HorstBaerbel/HubAlyzer/HubAlyzer/approx.h

#pragma once

#include <utility>
#include <cmath>

// == 1 / log2(10)
#define ONE_OVER_LOG2_10 0.3010299956639812f

// compute log10(x) by reducing x to [0.75, 1.5), then divide by log2(10)
// See: https://tech.ebayinc.com/engineering/fast-approximate-logarithms-part-iii-the-formulas/
// This version uses only multiplies
float log10f_fast(float x)
{
    constexpr float a = 0.338531;
    constexpr float b = -0.741619;
    constexpr float c = 1.445866;
#define FNM fexp + (((a * signif) + b) * signif + c) * signif

    float signif, fexp;
    int exp;
    float lg2;
    union {
        float f;
        unsigned int i;
    } ux1, ux2;
    int greater; // really a boolean
    /* 
     * Assume IEEE representation, which is sgn(1):exp(8):frac(23)
     * representing (1+frac)*2^(exp-127).  Call 1+frac the significand
     */

    // get exponent
    ux1.f = x;
    exp = (ux1.i & 0x7F800000) >> 23;
    // actual exponent is exp-127, will subtract 127 later

    greater = ux1.i & 0x00400000; // true if signif > 1.5
    if (greater)
    {
        // signif >= 1.5 so need to divide by 2.  Accomplish this by
        // stuffing exp = 126 which corresponds to an exponent of -1
        ux2.i = (ux1.i & 0x007FFFFF) | 0x3f000000;
        signif = ux2.f;
        fexp = exp - 126; // 126 instead of 127 compensates for division by 2
        signif = signif - 1.0;
        lg2 = FNM;
    }
    else
    {
        // get signif by stuffing exp = 127 which corresponds to an exponent of 0
        ux2.i = (ux1.i & 0x007FFFFF) | 0x3f800000;
        signif = ux2.f;
        fexp = exp - 127;
        signif = signif - 1.0;
        lg2 = FNM;
    }
    // last two lines of each branch are common code, but optimize better
    // when duplicated, at least when using gcc
    return lg2 * ONE_OVER_LOG2_10;
}

// Compute sin(x) and cos(x) with x in radians
std::pair<float, float> sincosf_fast(float x)
{
    // 256 sine values + 64 for cosine + one value added to front and back for safe interpolation
    static const float sintab[1+256+64+1] = {
      -0.0098480936, 0, 0.0246181448, 0.0492213673, 0.0737947547, 0.0983234116, 0.1227924704, 0.1471870991, 0.1714925112, 0.1956939739, 0.2197768177, 0.2437264449, 
      0.2675283385, 0.2911680713, 0.3146313139, 0.3379038444, 0.3609715563, 0.383820467, 0.4064367269, 0.4288066273, 0.4509166088, 0.4727532694, 
      0.494303373, 0.5155538572, 0.536491841, 0.557104633, 0.5773797389, 0.597304869, 0.6168679458, 0.6360571113, 0.6548607339, 0.6732674161, 
      0.6912660007, 0.7088455779, 0.7259954919, 0.7427053475, 0.758965016, 0.7747646418, 0.7900946479, 0.8049457422, 0.8193089227, 0.8331754833, 
      0.8465370188, 0.8593854302, 0.8717129295, 0.8835120444, 0.8947756231, 0.905496838, 0.9156691907, 0.9252865151, 0.9343429819, 0.9428331014, 
      0.9507517274, 0.9580940601, 0.964855649, 0.9710323955, 0.9766205557, 0.9816167423, 0.986017927, 0.9898214419, 0.9930249816, 0.9956266042, 
      0.9976247329, 0.9990181564, 0.9998060301, 0.9999878765, 0.9995635854, 0.9985334139, 0.9968979864, 0.9946582943, 0.9918156952, 0.988371912, 
      0.9843290322, 0.9796895064, 0.9744561468, 0.9686321256, 0.9622209729, 0.9552265749, 0.9476531712, 0.9395053523, 0.9307880571, 0.9215065694, 
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
      int i = static_cast<int>(floor(y));
      // get distance from left and right value
      auto d0 = y - floor(y);
      auto d1 = 1.0f - d0;
      auto s = d0 * sintab[i] + d1 * sintab[i + 1];
      auto c = d0 * sintab[i + 64] + d1 * sintab[i + 65];
      return std::make_pair(s, c);
}
