HorstBaerbel/HubAlyzer/HubAlyzer/serial_printf.h

#pragma once

#include <cstdarg>

/*
 * From: https://gist.github.com/ridencww/4e5d10097fee0b0f7f6b
 * Simple printf for writing to an Arduino serial port.  Allows specifying Serial..Serial3.
 *
 * const HardwareSerial&, the serial port to use (Serial..Serial3)
 * const char* fmt, the formatting string followed by the data to be formatted
 *
 * int d = 65;
 * float f = 123.4567;
 * char* str = "Hello";
 * serial_printf(Serial, "<fmt>", d);
 *
 * Example:
 *   serial_printf(Serial, "Sensor %d is %o and reads %1f\n", d, d, f) will
 *   output "Sensor 65 is on and reads 123.5" to the serial port.
 *
 * Formatting strings <fmt>
 * %B    - binary (d = 0b1000001)
 * %b    - binary (d = 1000001)
 * %c    - character (s = H)
 * %d/%i - integer (d = 65)\
 * %f    - float (f = 123.45)
 * %3f   - float (f = 123.346) three decimal places specified by %3.
 * %o    - boolean on/off (d = On)
 * %s    - char* string (s = Hello)
 * %X    - hexidecimal (d = 0x41)
 * %x    - hexidecimal (d = 41)
 * %%    - escaped percent ("%")
 * Thanks goes to @alw1746 for his %.4f precision enhancement
 */
void Serial_printf(const char *fmt, ...)
{
    va_list argv;
    va_start(argv, fmt);

    for (int i = 0; fmt[i] != '\0'; i++)
    {
        if (fmt[i] == '%')
        {
            // Look for specification of number of decimal places
            int places = 2;
            if (fmt[i + 1] == '.')
                i++; // alw1746: Allows %.4f precision like in stdio printf (%4f will still work).
            if (fmt[i + 1] >= '0' && fmt[i + 1] <= '9')
            {
                places = fmt[i + 1] - '0';
                i++;
            }

            switch (fmt[++i])
            {
            case 'B':
                Serial.print("0b"); // Fall through intended
            case 'b':
                Serial.print(va_arg(argv, int), BIN);
                break;
            case 'c':
                Serial.print((char)va_arg(argv, int));
                break;
            case 'd':
            case 'i':
                Serial.print(va_arg(argv, int), DEC);
                break;
            case 'f':
                Serial.print(va_arg(argv, double), places);
                break;
            case 'l':
                Serial.print(va_arg(argv, long), DEC);
                break;
            case 'o':
                Serial.print(va_arg(argv, int) == 0 ? "off" : "on");
                break;
            case 's':
                Serial.print(va_arg(argv, const char *));
                break;
            case 'X':
                Serial.print("0x"); // Fall through intended
            case 'x':
                Serial.print(va_arg(argv, int), HEX);
                break;
            case '%':
                Serial.print(fmt[i]);
                break;
            default:
                Serial.print("?");
                break;
            }
        }
        else
        {
            Serial.print(fmt[i]);
        }
    }
    va_end(argv);
}
